colinleroy/BurgerDisk/PCB/BDisk.png

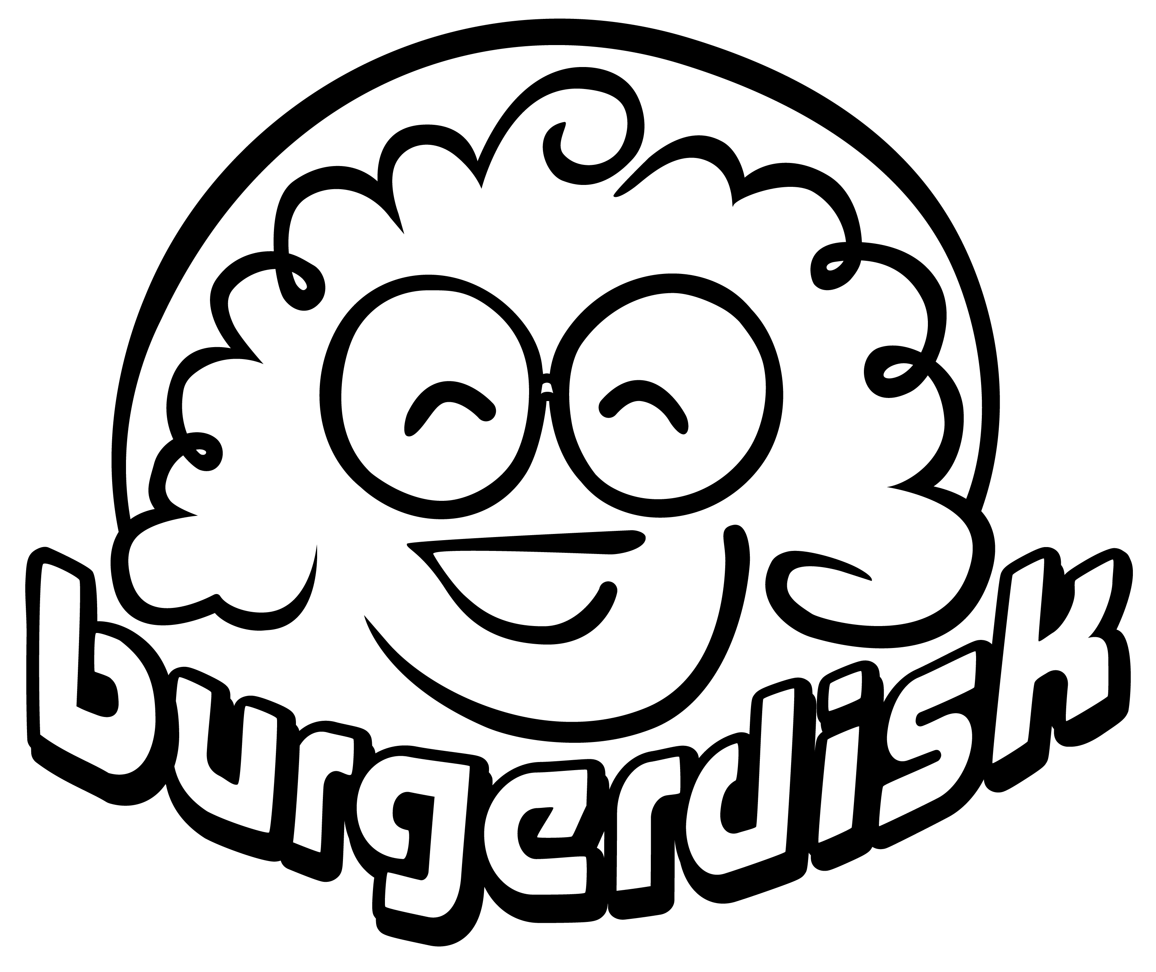
PCB/BDisk.png
