colinleroy/BurgerDisk/PCB/DominoDisk-THT/Smallest.png

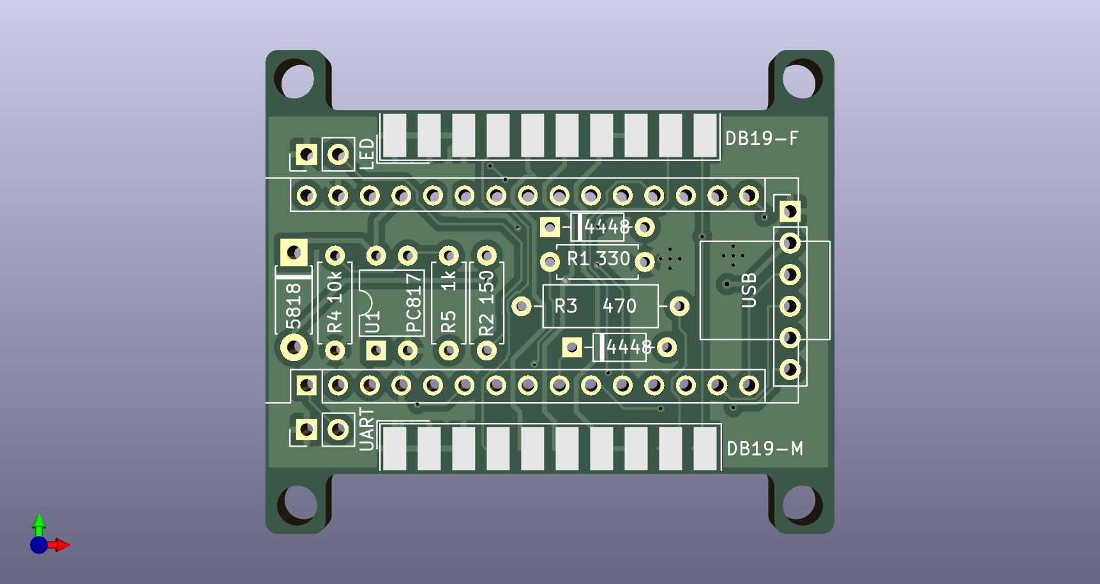
PCB/DominoDisk-THT/Smallest.png
