colinleroy/BurgerDisk/build_instructions/pictures/arduino_programming_port_soldering.jpeg

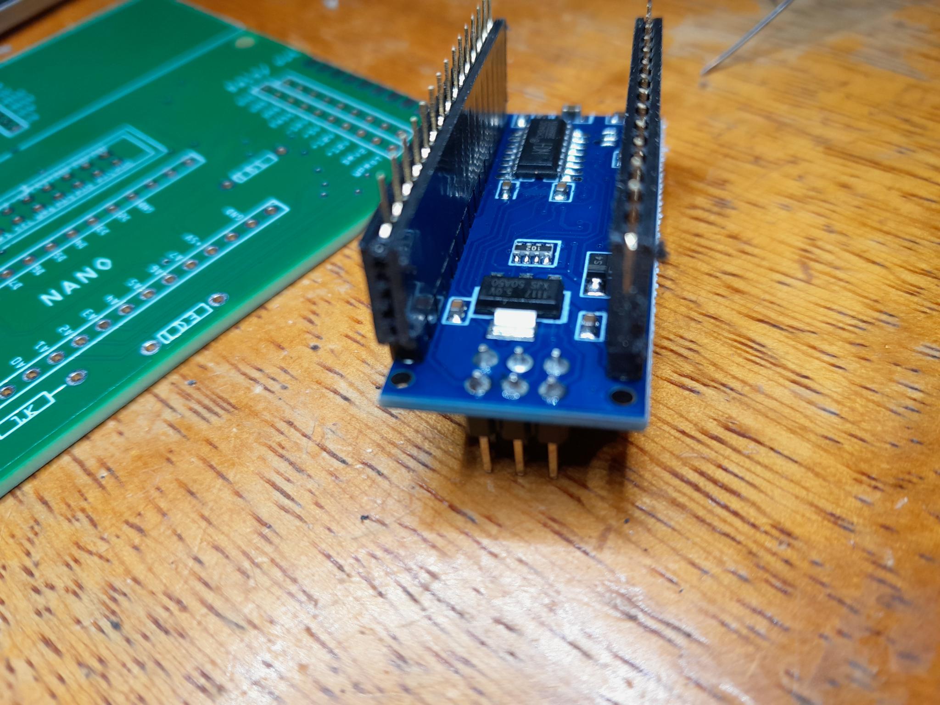
build_instructions/pictures/arduino_programming_port_soldering.jpeg
