colinleroy/BurgerDisk/build_instructions/pictures/fujinet-db19-adapter.png

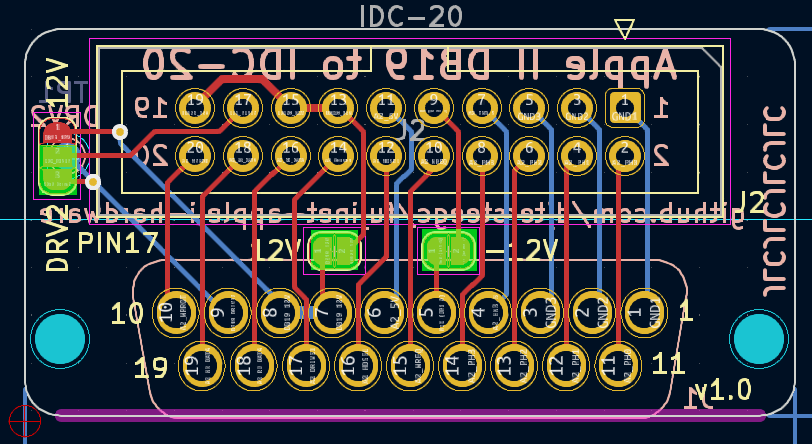
build_instructions/pictures/fujinet-db19-adapter.png
