colinleroy/BurgerDisk/build_instructions/pictures/male_female_arduino_headers_assembly.jpeg

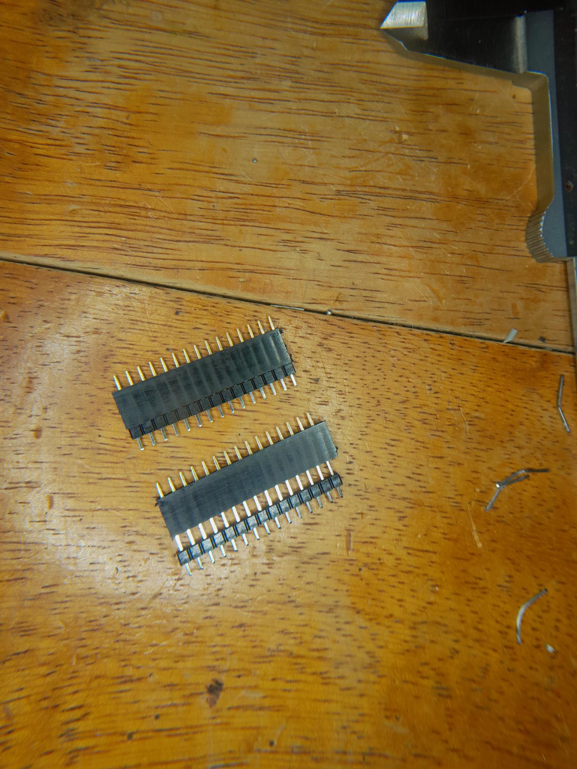
build_instructions/pictures/male_female_arduino_headers_assembly.jpeg
