colinleroy/BurgerDisk/build_instructions/pictures/mini-upgrade/header-tinning.jpeg

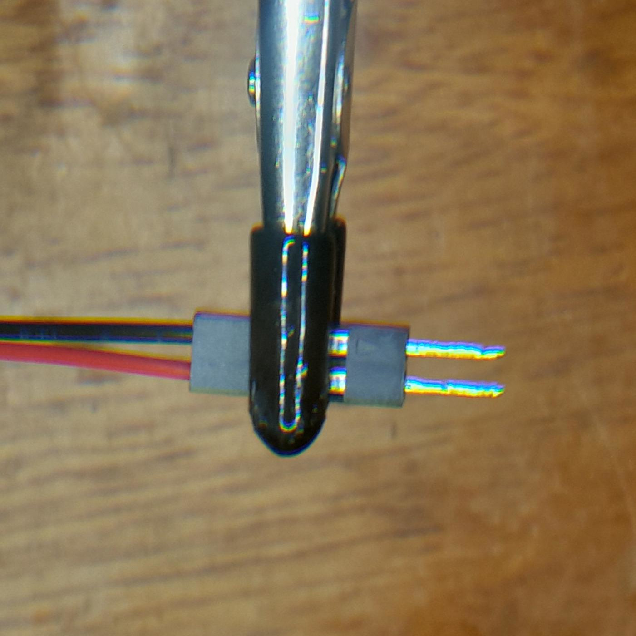
build_instructions/pictures/mini-upgrade/header-tinning.jpeg
