colinleroy/BurgerDisk/build_instructions/pictures/pcb-v2.0-soldered.jpeg

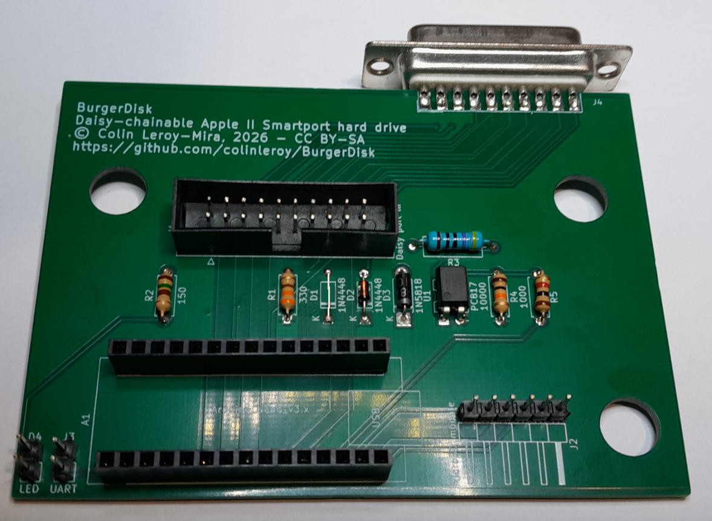
build_instructions/pictures/pcb-v2.0-soldered.jpeg
