colinleroy/BurgerDisk/build_instructions/pictures/PCB-v2.0.jpeg

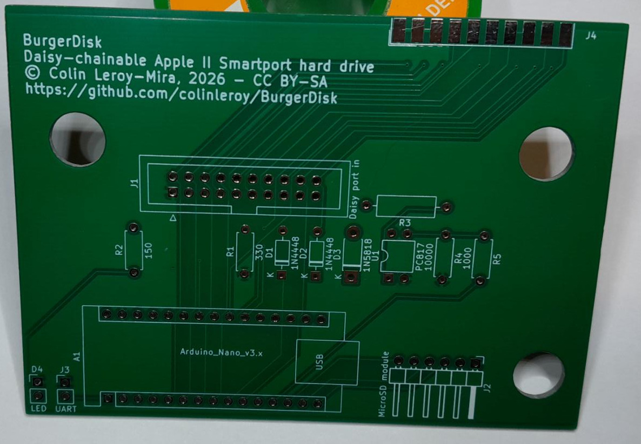
build_instructions/pictures/PCB-v2.0.jpeg
