colinleroy/BurgerDisk/build_instructions/pictures/positioning_arduino_headers.jpeg

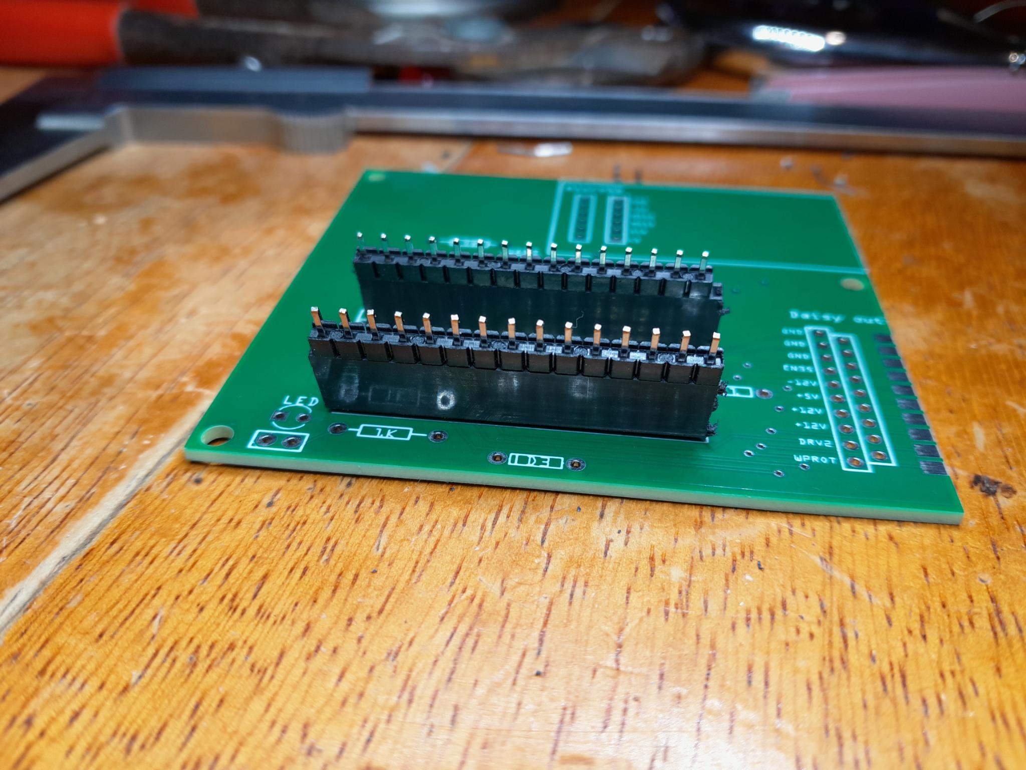
build_instructions/pictures/positioning_arduino_headers.jpeg
