colinleroy/BurgerDisk/build_instructions/pictures/soldering_arduino_on_headers.jpeg

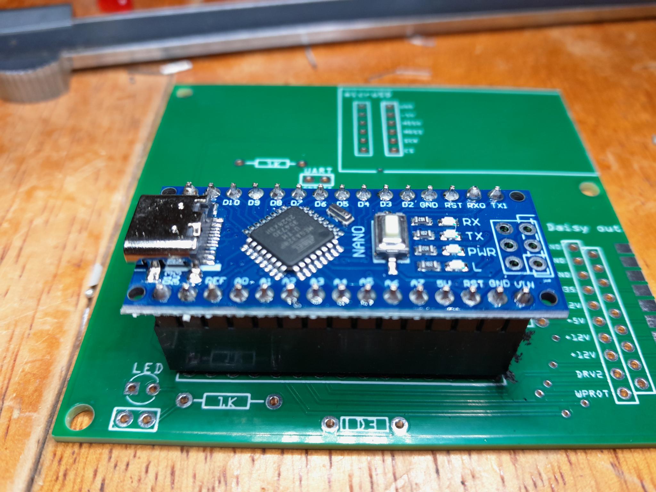
build_instructions/pictures/soldering_arduino_on_headers.jpeg
