colinleroy/BurgerDisk/PCB/DominoDisk/DominoDisk.kicad_pcb

## KiCad design PCB/DominoDisk/DominoDisk.kicad_pcb (2026-02-11)

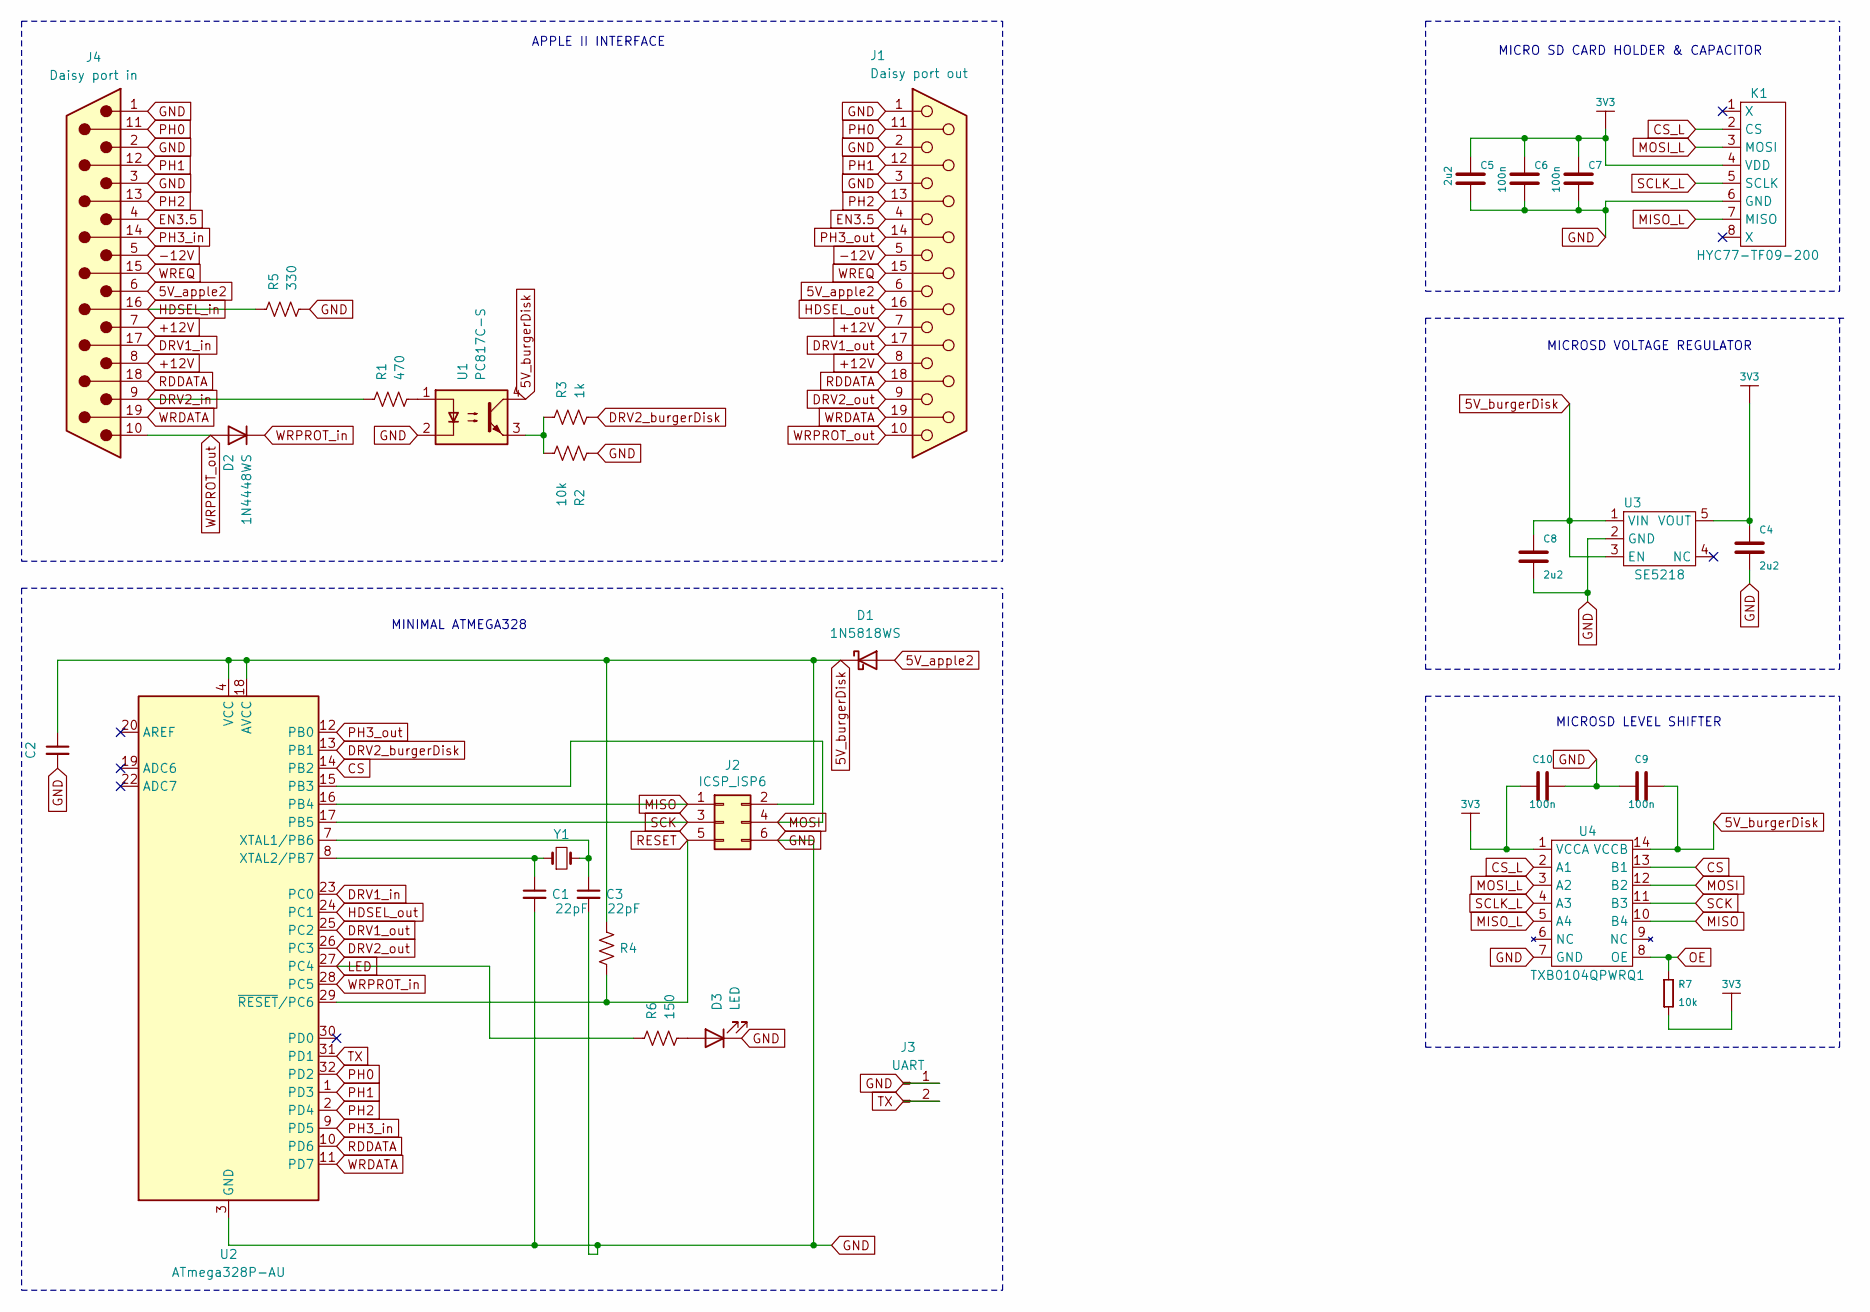
[picture p74: schematic DominoDisk.kicad_sch, DominoDisk - very small Apple II hard drive]

Parts:
C1, C3: 22pF; C_0603_1608Metric; LCSC C1804
C2: 100nF; C_0603_1608Metric; LCSC C28233
C4, C5, C8: 2u2; C_0603_1608Metric; LCSC C1607
C6, C7, C9, C10: 100n; C_0603_1608Metric; LCSC C1590
D1: 1N5818WS; D_SOD-323; LCSC C5240366
D2: 1N4448WS; D_SOD-323F; LCSC C167101
D3: LED; LED_0603_1608Metric; LCSC C2288
J1: Daisy port out; DSUB-19_Female_EdgeMount_Pitch2.77mm
J2: ICSP_ISP6; IDC-Header_2x03_P2.54mm_Vertical_SMD; LCSC C192301
J3: UART; PinHeader_1x02_P2.54mm_Vertical; LCSC C6273326
J4: Daisy port in; DSUB-19_Male_EdgeMount_Pitch2.77mm
K1: HYC77-TF09-200; MICROSD-HYC77-TF09-200; LCSC C341092
R1: 470; R_1206_3216Metric; LCSC C137212
R2, R7: 10k; R_0603_1608Metric; LCSC C177337
R3: 1k; R_0603_1608Metric; LCSC C177343
R4: 10K; R_0603_1608Metric; LCSC C17414
R5: 330; R_0603_1608Metric; LCSC C177341
R6: 150; R_0603_1608Metric; LCSC C177290
U1: PC817C-S; SOP-4_3.8x4.1mm_P2.54mm; LCSC C3008369
U2: ATmega328P-AU; TQFP-32_7x7mm_P0.8mm; LCSC C14877
U3: SE5218; SOT-23-5; LCSC C118233
U4: TXB0104QPWRQ1; TSSOP-14-1EP_4.4x5mm_P0.65mm; LCSC C527571
Y1: 16MHz; Crystal_SMD_HC49-SD; LCSC C12676

Connections:
3V3: C4.2, C5.2, C6.2, C7.2, C10.1, K1.4 (VDD), R7.1, U3.5 (VOUT), U4.1 (VCCA)
5V_apple2: D1.2 (A), J1.6, J4.6
5V_burgerDisk: C2.1, C8.2, C9.2, D1.1 (K), J2.2, R4.1, U1.4, U2.4 (VCC), U2.6 (VCC), U2.18 (AVCC), U3.1 (VIN), U3.3 (EN), U4.14 (VCCB)
+12V: J1.7, J1.8, J4.7, J4.8
-12V: J1.5, J4.5
CS: U2.14 (PB2), U4.13 (B1)
CS_L: K1.2 (CS), U4.2 (A1)
DRV1_in: J4.17, U2.23 (PC0)
DRV1_out: J1.17, U2.25 (PC2)
DRV2_burgerDisk: R3.1, U2.13 (PB1)
DRV2_in: J4.9, R1.1
DRV2_out: J1.9, U2.26 (PC3)
EN3.5: J1.4, J4.4
GND: C1.2, C2.2, C3.2, C4.1, C5.1, C6.1, C7.1, C8.1, C9.1, C10.2, D3.1 (K), J1.1, J1.2, J1.3, J2.6, J3.1, J4.1, J4.2, J4.3, K1.6 (GND), R2.1, R5.1, U1.2, U2.3 (GND), U2.5 (GND), U2.21 (GND), U3.2 (GND), U4.7 (GND)
HDSEL_in: J4.16, R5.2
HDSEL_out: J1.16, U2.24 (PC1)
LED: R6.2, U2.27 (PC4)
MISO: J2.1, U2.16 (PB4), U4.10 (B4)
MISO_L: K1.7 (MISO), U4.5 (A4)
MOSI: J2.4, U2.15 (PB3), U4.12 (B2)
MOSI_L: K1.3 (MOSI), U4.3 (A2)
unnamed: D3.2 (A), R6.1
unnamed: R1.2, U1.1
unnamed: R2.2, R3.2, U1.3
unnamed: C3.1, U2.7 (XTAL1/PB6), Y1.2
unnamed: C1.1, U2.8 (XTAL2/PB7), Y1.1
OE: R7.2, U4.8 (OE)
PH0: J1.11, J4.11, U2.32 (PD2)
PH1: J1.12, J4.12, U2.1 (PD3)
PH2: J1.13, J4.13, U2.2 (PD4)
PH3_in: J4.14, U2.9 (PD5)
PH3_out: J1.14, U2.12 (PB0)
RDDATA: J1.18, J4.18, U2.10 (PD6)
RESET: J2.5, R4.2, U2.29 (~RESET/PC6)
SCK: J2.3, U2.17 (PB5), U4.11 (B3)
SCLK_L: K1.5 (SCLK), U4.4 (A3)
TX: J3.2, U2.31 (PD1)
WRDATA: J1.19, J4.19, U2.11 (PD7)
WREQ: J1.15, J4.15
WRPROT_in: D2.1 (K), U2.28 (PC5)
WRPROT_out: D2.2 (A), J1.10, J4.10

Notes on the sheet:
MICROSD LEVEL SHIFTER
MINIMAL ATMEGA328
MICROSD VOLTAGE REGULATOR
APPLE II INTERFACE
MICRO SD CARD HOLDER & CAPACITOR

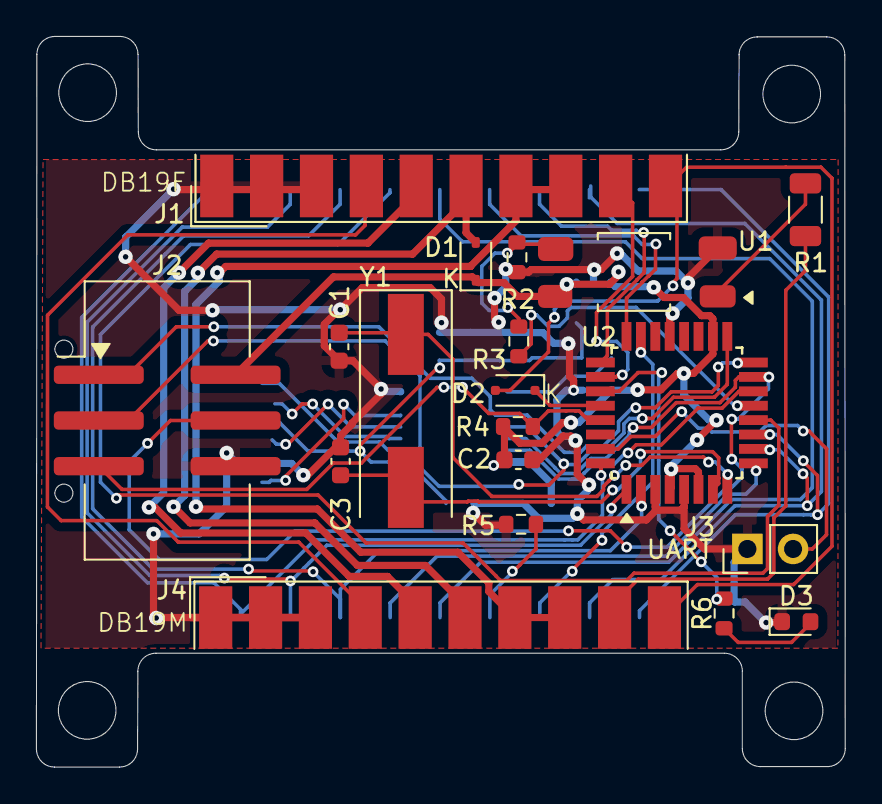
[picture p75: board DominoDisk.kicad_pcb from above]

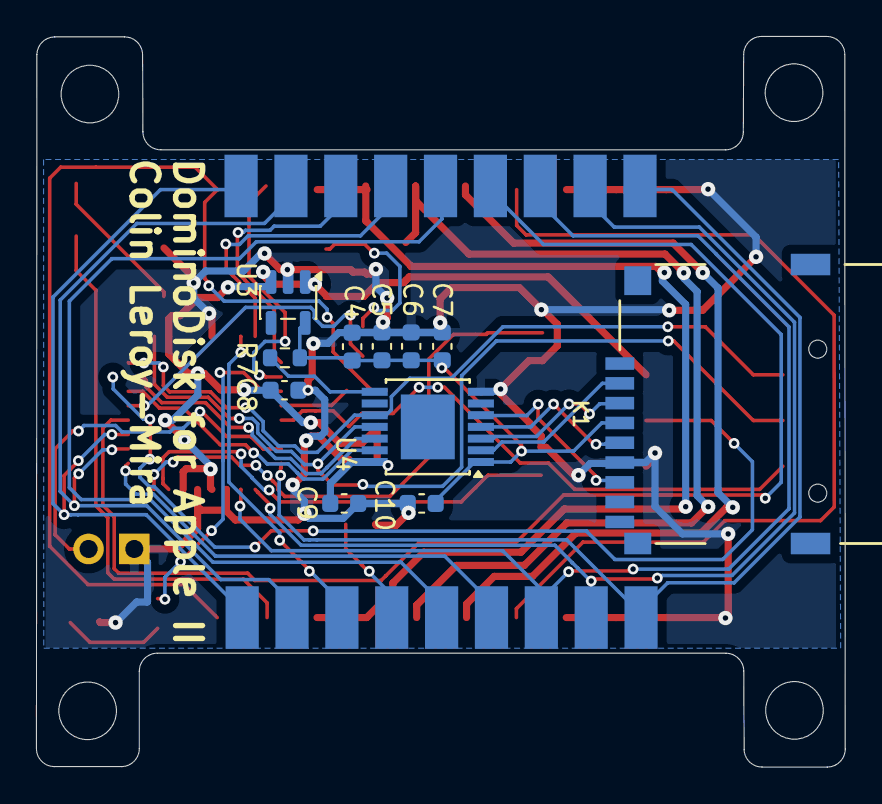
[picture p76: board DominoDisk.kicad_pcb from below]

Board: 2 copper layers, 44.9 x 40.6 mm, 30 parts (11 on the bottom side), 41 nets.
