colinleroy/BurgerDisk/firmware/packet_codecs.c

//*****************************************************************************
//
// Apple //c Smartport Compact Flash adapter
// Written by Robert Justice  email: rjustice(at)internode.on.net
//
// Packet encoding and decoding routines.
//
// MIT-licensed:
//
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
// Doc: http://www.applelogic.org/files/GSFIRMWAREREF1.pdf
//
//*****************************************************************************

#include <string.h>
#include "sp_vals.h"

extern unsigned char *packet_buffer;

static void init_packet_buffer(unsigned char source) {
  packet_buffer[0] = 0xff;  //sync bytes
  packet_buffer[1] = 0x3f;
  packet_buffer[2] = 0xcf;
  packet_buffer[3] = 0xf3;
  packet_buffer[4] = 0xfc;
  packet_buffer[5] = 0xff;
  packet_buffer[6] = 0xc3;  //PBEGIN - start byte
  packet_buffer[7] = 0x80;  //DEST - dest id - host
  packet_buffer[8] = source; //SRC - source id - us
}

//*****************************************************************************
// Function: encode_data_packet
// Parameters: source id
// Returns: none
//
// Description: encode 512 byte data packet for read block command from host
// requires the data to be in the packet buffer, and builds the smartport
// packet IN PLACE in the packet buffer
//*****************************************************************************
void encode_data_packet (unsigned char source, SP_Error status)
{
  int count;
  signed char grpbyte, grpcount;
  unsigned char checksum = 0, grpmsb;
  unsigned char *src, *dst;

  // Calculate checksum of sector bytes before we destroy them
  for (count = 0; count < 512; count++) {
    // xor all the data bytes
    checksum ^= packet_buffer[count];
  }

  // Start assembling the packet at the rear and work
  // your way to the front so we don't overwrite data
  // we haven't encoded yet

  //grps of 7
  src = packet_buffer + (73*7);
  dst = packet_buffer + 16 + 7 + (72*8);
  for (grpcount = 73; grpcount > 0; grpcount--) {
    grpmsb = 0;
    for (grpbyte = 7; grpbyte > 0; grpbyte--) {
      // compute msb group byte
      grpmsb = grpmsb | ((*src >> (grpbyte)) & (0x80 >> (grpbyte)));
      // now add the group data bytes bits 6-0
      *dst-- = *(src--) | 0x80;
    }
    *dst-- = grpmsb | 0x80;
  }
  //odd byte
  packet_buffer[14] = ((packet_buffer[0] >> 1) & 0x40) | 0x80;
  packet_buffer[15] = packet_buffer[0] | 0x80;

  init_packet_buffer(source);
  packet_buffer[9]  = 0x82; //TYPE DATA
  packet_buffer[10] = 0x80; //AUX
  packet_buffer[11] = 0x80 | status; //STAT
  packet_buffer[12] = 0x81; //ODDCNT  - 1 odd byte for 512 byte packet
  packet_buffer[13] = 0xC9; //GRP7CNT - 73 groups of 7 bytes for 512 byte packet

  // xor the packet header bytes
  for (count = 7; count < 14; count++) {
    checksum ^= packet_buffer[count];
  }

  packet_buffer[600] = checksum | 0xaa;      // 1 c6 1 c4 1 c2 1 c0
  packet_buffer[601] = checksum >> 1 | 0xaa; // 1 c7 1 c5 1 c3 1 c1

  //end bytes
  packet_buffer[602] = 0xc8;  //pkt end
  packet_buffer[603] = 0x00;  //mark the end of the packet_buffer
}

//*****************************************************************************
// Function: encode_write_status_packet
// Parameters: source,status
// Returns: none
//
// Description: this is the reply to the write block data packet. The reply
// indicates the status of the write block cmd.
//*****************************************************************************
void encode_write_status_packet(unsigned char source, SP_Error status)
{
  unsigned char count;
  unsigned char checksum = 0;

  init_packet_buffer(source);
  packet_buffer[9]  = 0x81; //TYPE
  packet_buffer[10] = 0x80; //AUX
  packet_buffer[11] = 0x80 | status; //STAT
  packet_buffer[12] = 0x80; //ODDCNT
  packet_buffer[13] = 0x80; //GRP7CNT

  // xor the packet header bytes
  for (count = 7; count < 14; count++) {
    checksum = checksum ^ packet_buffer[count];
  }

  packet_buffer[14] = checksum | 0xaa;      // 1 c6 1 c4 1 c2 1 c0
  packet_buffer[15] = checksum >> 1 | 0xaa; // 1 c7 1 c5 1 c3 1 c1

  packet_buffer[16] = 0xc8;  //pkt end
  packet_buffer[17] = 0x00;  //mark the end of the packet_buffer
}

//*****************************************************************************
// Function: encode_init_reply_packet
// Parameters: source
// Returns: none
//
// Description: this is the reply to the init command packet. A reply indicates
// the original dest id has a device on the bus. If the STAT byte is 0, (0x80)
// then this is not the last device in the chain. This is written to support up
// to 4 partions, i.e. devices, so we need to specify when we are doing the last
// init reply.
//*****************************************************************************
void encode_init_reply_packet (unsigned char source, SP_Error status)
{
  unsigned char count;
  unsigned char checksum = 0;

  init_packet_buffer(source);
  packet_buffer[9]  = 0x80; //TYPE
  packet_buffer[10] = 0x80; //AUX
  packet_buffer[11] = 0x80 | status; //STAT - data status
  packet_buffer[12] = 0x80; //ODDCNT
  packet_buffer[13] = 0x80; //GRP7CNT

  // xor the packet header bytes
  for (count = 7; count < 14; count++) {
    checksum = checksum ^ packet_buffer[count];
  }
  packet_buffer[14] = checksum | 0xaa;      // 1 c6 1 c4 1 c2 1 c0
  packet_buffer[15] = checksum >> 1 | 0xaa; // 1 c7 1 c5 1 c3 1 c1

  packet_buffer[16] = 0xc8; //PEND
  packet_buffer[17] = 0x00; //end of packet in buffer
}

//*****************************************************************************
// Function: encode_status_reply_packet
// Parameters: source
// Returns: none
//
// Description: this is the reply to the status command packet. The reply
// includes following:
// data byte 1 is general info.
// data byte 2-4 number of blocks. 2 is the LSB and 4 the MSB.
// Size determined from image file.
//*****************************************************************************
void encode_status_reply_packet (unsigned char device_id, unsigned char err, unsigned long blocks)
{
  unsigned char count;
  unsigned char checksum = 0;
  unsigned char data[5];

  //Build the contents of the packet
  //Info byte
  //Bit 7: Block  device
  //Bit 6: Write allowed
  //Bit 5: Read allowed
  //Bit 4: Device online or disk in drive
  //Bit 3: Format allowed
  //Bit 2: Media write protected
  //Bit 1: Currently interrupting (//c only)
  //Bit 0: Currently open (char devices only)
  data[0] = blocks > 0 ? 0b11111000 : 0b11101000;
  //Disk size
  data[1] = blocks & 0xff;
  data[2] = (blocks >> 8 ) & 0xff;
  data[3] = (blocks >> 16 ) & 0xff;

  //calc the data bytes checksum
  for(count = 0; count < 4; count++) {
    checksum ^= data[count];
  }

  init_packet_buffer(device_id);
  packet_buffer[9]  = 0x81; //TYPE -status
  packet_buffer[10] = 0x80; //AUX
  packet_buffer[11] = 0x80 | err; //STAT - data status
  packet_buffer[12] = 0x84; //ODDCNT - 4 data bytes
  packet_buffer[13] = 0x80; //GRP7CNT

  // xor the packet header bytes
  for (count = 7; count < 14; count++) {
    checksum = checksum ^ packet_buffer[count];
  }

  // odd bytes MSBs
  packet_buffer[14] = 0x80 
                      | ((data[0]>>1) & 0x40) 
                      | ((data[1]>>2) & 0x20) 
                      | ((data[2]>>3) & 0x10) 
                      | ((data[3]>>4) & 0x08);

  packet_buffer[15] = data[0] | 0x80;
  packet_buffer[16] = data[1] | 0x80;
  packet_buffer[17] = data[2] | 0x80;
  packet_buffer[18] = data[3] | 0x80;

  packet_buffer[19] = checksum | 0xaa;      // 1 c6 1 c4 1 c2 1 c0
  packet_buffer[20] = checksum >> 1 | 0xaa; // 1 c7 1 c5 1 c3 1 c1

  packet_buffer[21] = 0xc8; //PEND
  packet_buffer[22] = 0x00; //end of packet in buffer
}

//*****************************************************************************
// Function: encode_status_dib_reply_packet
// Parameters: source
// Returns: none
//
// Description: this is the reply to the status command 03 packet. The reply
// includes following:
// data byte 1
// data byte 2-4 number of blocks. 2 is the LSB and 4 the MSB.
// Calculated from actual image file size.
//*****************************************************************************
void encode_status_dib_reply_packet (unsigned char device_id, unsigned long blocks)
{
  int grpbyte, grpcount, i, count;
  int grpnum, oddnum;
  unsigned char checksum = 0, grpmsb;
  unsigned char group_buffer[7];
  unsigned char data[26];
  //data buffer: 3 x Grp7 + 4 or 5 odds
  grpnum = 3;
  oddnum = 4;

  i = 0;
  //* write data buffer first (25 bytes) 3 grp7 + 4 odds
  data[i++] = blocks > 0 ? 0b11111000 : 0b11101000;
  //number of blocks =0x00ffff = 65525 or 32mb
  data[i++]  = blocks & 0xff; //block size 1
  data[i++]  = (blocks >> 8 ) & 0xff; //block size 2
  data[i++]  = (blocks >> 16 ) & 0xff ; //block size 3
  data[i++] = 14; //ID string length - 14 chars
  data[i++] = 'B';
  data[i++] = 'U';
  data[i++] = 'R';
  data[i++] = 'G';
  data[i++] = 'E';
  data[i++] = 'R';
  data[i++] = 'D';
  data[i++] = 'I';
  data[i++] = 'S';
  data[i++] = 'K';
  data[i++] = identifier;
  data[i++] = ' ';
  data[i++] = ' ';
  data[i++] = ' ';
  data[i++] = ' ';
  data[i++] = ' ';  //ID string (16 chars total)
  data[i++] = 0x02; //Device type    - 0x02  harddisk
  data[i++] = 0x00; //Device Subtype - 0x00 Removable media
  data[i++] = 0x01; //Firmware version 2 bytes
  data[i++] = 0x0f; //

  // Calculate checksum of sector bytes before we destroy them
  for (count = 0; count < i; count++) {
    checksum = checksum ^ data[count];
  }

  // Start assembling the packet at the rear and work
  // your way to the front so we don't overwrite data
  // we haven't encoded yet

  //grps of 7
  for (grpcount = grpnum-1; grpcount >= 0; grpcount--) // 3
  {
    for (i = 0;i < 7;i++) {
      group_buffer[i]=data[i + oddnum + (grpcount * 7)];
    }
    // add group msb byte
    grpmsb = 0;
    for (grpbyte = 0; grpbyte < 7; grpbyte++) {
      grpmsb = grpmsb | ((group_buffer[grpbyte] >> (grpbyte + 1)) & (0x80 >> (grpbyte + 1)));
    }
    packet_buffer[(14 + oddnum + 1) + (grpcount * 8)] = grpmsb | 0x80; // set msb to one

    // now add the group data bytes bits 6-0
    for (grpbyte = 0; grpbyte < 7; grpbyte++) {
      packet_buffer[(14 + oddnum + 2) + (grpcount * 8) + grpbyte] = group_buffer[grpbyte] | 0x80;
    }
  }

  init_packet_buffer(device_id);
  packet_buffer[9]  = 0x81; //TYPE -status
  packet_buffer[10] = 0x80; //AUX
  packet_buffer[11] = 0x80; //STAT - data status
  packet_buffer[12] = 0x80|oddnum; //ODDCNT - 4 or 5 data bytes
  packet_buffer[13] = 0x80|grpnum; //GRP7CNT - 3 grps of 7

  //odd bytes high bits
  packet_buffer[14] = 0x80 
                    | ((data[0]>> 1) & 0x40)
                    | ((data[1]>>2) & 0x20)
                    | ((data[2]>>3) & 0x10)
                    | ((data[3]>>4) & 0x08);

  packet_buffer[15] = data[0] | 0x80;
  packet_buffer[16] = data[1] | 0x80;
  packet_buffer[17] = data[2] | 0x80;
  packet_buffer[18] = data[3] | 0x80;

  // xor the packet header bytes
  for (count = 7; count < 14; count++) {
    checksum = checksum ^ packet_buffer[count];
  }

  // finish packet
  packet_buffer[43] = checksum | 0xaa;      // 1 c6 1 c4 1 c2 1 c0
  packet_buffer[44] = checksum >> 1 | 0xaa; // 1 c7 1 c5 1 c3 1 c1

  packet_buffer[45] = 0xc8; //PEND
  packet_buffer[46] = 0x00; //end of packet in buffer
}
